wyolum/1sqinch555/fabricate/1sqinch555_02.png

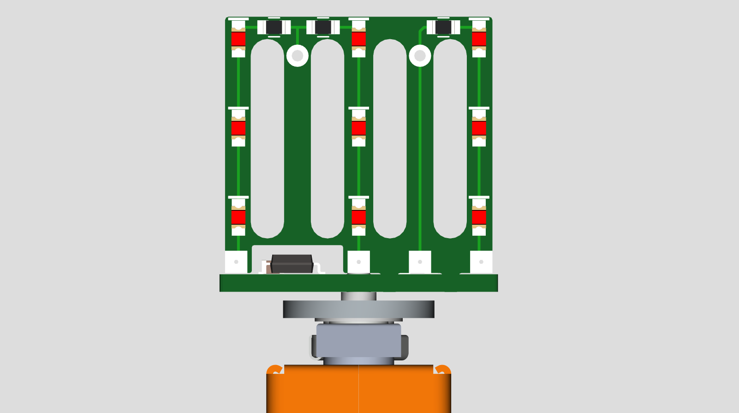
fabricate/1sqinch555_02.png
