wyolum/1sqinch555/fabricate/1sqinch555_05.png

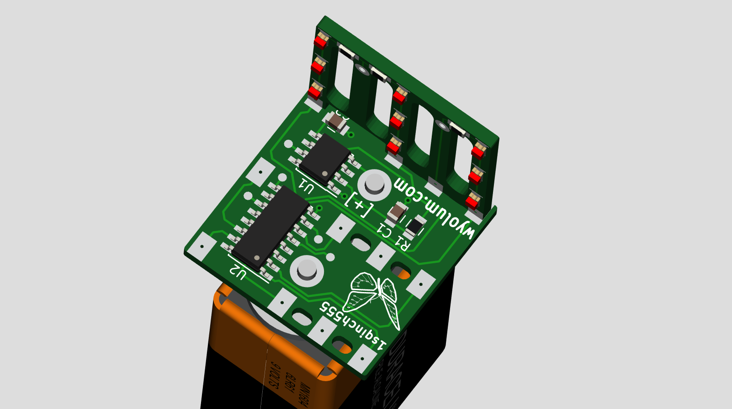
fabricate/1sqinch555_05.png
